D-sorganization/openflight_development/notes/2026-08-25-iwr6843-vs-kld7-upgrade-analysis.md

# Field Note: TI IWR6843 (60 GHz) vs K-LD7 (24 GHz) Upgrade Analysis

**Date:** 2026-08-25  
**Topic:** Quantitative Upgrade Significance Analysis & Upstream Discussion #161 Response  
**Author:** Dieter Olson (`dieterolson`)  
**Context:** Upstream [Discussion #161](https://github.com/jewbetcha/openflight/discussions/161) — "Is the IWR6843 upgrade significant?"

---

## 1. Executive Summary

Upstream builder `jtemple967` in Discussion #161 asked whether migrating from the dual K-LD7 radar setup to the TI IWR6843 mmWave radar is worth the effort and expense ("would be willing to upgrade if it's significant"). 

Based on empirical datasets from MLM2 Pro and TrackMan validation sessions, radar physical acoustics, and RF architecture analysis, the upgrade is **unambiguously significant**:

1. **2.58x Precision Improvement on Irons & Wedges:** Launch angle MAE improves from **2.14° (K-LD7)** to **0.83° (IWR6843)**, with a median absolute error of **0.67°**.
2. **Systematic Bias Elimination:** K-LD7 exhibited a persistent **+1.85°** upward bias; the IWR6843 LCMF-v1 pipeline centers at **-0.04°** (effectively zero bias).
3. **Driver Accuracy Improvement (3.38x):** Gated driver launch angle improves from **4.80° MAE (K-LD7)** to **1.42° MAE (IWR6843)**.
4. **Complete Physical RF Isolation:** Transitioning from 24 GHz K-band to 60 GHz V-band completely eliminates mutual RF interference and desensitization with the 24 GHz OPS243-A speed radar.
5. **Pre-Impact Club Path Extraction:** 12-channel MIMO allows 3D club path tracking (±1.18° RMSE runtime, ±0.3° fixture test), which was physically impossible with the K-LD7.
6. **Hardware & Enclosure Simplification:** 1 single board replaces 2 separate K-LD7 modules and 2 FTDI serial cables.

---

## 2. Comprehensive Hardware & RF Specifications

| Architectural Parameter | Dual K-LD7 (Deprecated) | TI IWR6843LEVM (Current Gen) | Physical Impact |
|---|---|---|---|
| **Carrier Frequency** | 24.125 GHz (K-Band) | 60.000 GHz (V-Band mmWave) | Wavelength drops from 12.4 mm to 5.0 mm; 2.5x finer spatial resolution |
| **Antenna Architecture** | 2 RX × 1 TX per unit | 4 RX × 3 TX MIMO Virtual Array | **12 virtual channels** vs single 1D phase baseline |
| **Field of View (Elevation)** | ±15° (30° span) | ±30° (60° span) | Easily captures high launch wedges (>30°) without beam clipping |
| **Field of View (Azimuth)** | ±15° (30° span) | ±60° (120° span) | Full lateral coverage for extreme pushes/pulls/shanks |
| **Doppler Resolution** | 0.85 m/s | 0.18 m/s | 4.7x finer velocity bins |
| **Velocity Aliasing Limit** | Aliased > 62 mph (100 km/h) | **Unaliased across full golf speed range (15–200+ mph)** | Eliminates fragile Doppler phase dealiasing algorithms |
| **OPS243 Coexistence** | High (both operate in 24 GHz K-band) | **Zero (60 GHz vs 24 GHz)** | Eliminates RF receiver saturation and mutual desensitization |
| **Capture Memory** | Coarse snapshot buffer over FTDI | 786 KB on-chip L3 rolling buffer | 72 ms coherent radar movie at ~4–6 ms cadence |
| **Physical Hardware** | 2 units + 2 FTDI UART bridges | 1 single board | Drastically cleaner enclosure and lower USB bus contention |

---

## 3. Empirical Accuracy Benchmarks (MLM2 Pro & TrackMan Referenced)

### 3.1 Headline Metric Summary

| Metric | Dual K-LD7 | TI IWR6843 | Delta / Improvement |
|---|---|---|---|
| **Iron/Wedge Launch Angle MAE** | 2.14° | **0.83°** | **2.58x accuracy improvement** |
| **Iron/Wedge Median Error (p50)** | 1.92° | **0.67°** | 2.87x error reduction |
| **Iron/Wedge 90th Percentile Error (p90)** | 3.95° | **1.80°** | Outliers cut by >2° |
| **Systematic Launch Bias** | +1.85° | **-0.04°** | Zero systematic bias |
| **Strict Coverage (Clean Reads)** | 72.4% | **87.4%** | +15.0% higher clean read yield |
| **Driver Launch Angle MAE (Speed-Gated)** | 4.80° | **1.42°** | **3.38x accuracy improvement** |
| **Azimuth / Launch Direction RMSE** | ±2.85° | **±1.10°** | 2.6x tighter horizontal resolution |
| **Club Path Tracking** | Unsupported | **±1.18° RMSE** | New capability |
| **Indoor Multipath Handling** | Severe ground bounce phase error | **LCMF-v1 spatial filter** | Multipath modeled and rejected |

---

### 3.2 Per-Club Empirical Breakdown

Field data captured across indoor TrackMan and MLM2 Pro cross-validation sessions:

| Club Group | Total Swings | Covered Shots | Coverage % | Launch MAE | p50 (Median) | p75 | p90 | Systematic Bias |
|---|---|---|---|---|---|---|---|---|
| **Sand Wedge** | 17 | 15 | 88.2% | **0.67°** | 0.46° | 1.06° | 1.58° | -0.22° |
| **9-Iron** | 27 | 25 | 92.6% | **0.89°** | 0.81° | 1.18° | 1.73° | +0.24° |
| **7-Iron** | 21 | 18 | 85.7% | **0.91°** | 0.49° | 1.15° | 1.88° | -0.06° |
| **5-Iron** | 22 | 18 | 81.8% | **0.82°** | 0.69° | 1.31° | 1.84° | -0.25° |
| **Driver (Raw / Ungated)** | 22 | 18 | 81.8% | 3.55° | 1.31° | 1.82° | 15.57° | +3.39° |
| **Driver (Speed-Gated)** | 22 | 15 | 68.2% | **1.42°** | 1.10° | 1.65° | 2.40° | +0.45° |
| **Mis-Hits / High Clutter** | 19 | 13 | 68.4% | **2.20°** | 1.16° | 3.07° | 5.10° | -0.54° |

---

### 3.3 Angle Source & Confidence Tier Split

The IWR6843 pipeline uses an explicit three-tier confidence architecture:

| Tier | Source / Mode | Description | Coverage | MAE | UI Representation |
|---|---|---|---|---|---|
| **Tier 1** | **Strict LCMF-v1** | High-confidence 5-model consensus over 12–18 frames in L3 buffer | 87.4% (76/87) | **0.83°** | **3 dots** (Full Confidence Measured) |
| **Tier 2** | **Relaxed RMS (≤ 0.58)** | Secondary recovery for noisier tracks passing speed & frame continuity | 85.7% (42/49) | **1.00°** | **2 dots** (Measured, Lower Confidence) |
| **Tier 2b** | **Relaxed RMS (≤ 0.70)** | Broadest recovery lane in high-clutter net environments | 91.8% (45/49) | **1.09°** | **2 dots** (Lab / Diagnostic Mode) |
| **Tier 3** | **Fallback Estimate** | Club/speed lookup table when radar movie is inconclusive | 12.6% (11/87) | **3.20°** | **1 dot / text** (Estimated) |

---

## 4. Deep-Dive: Driver Ghost-Track Gating

Why does the raw driver launch angle have a 3.55° MAE while irons achieve 0.83° MAE?

### Root Cause
Driver swings generate high-speed ball flight (140–170 mph) and large club head returns. In short indoor net cages (6–10 ft), the ball traverses the radar field in under 30 ms. In a subset of driver shots, weak radar echoes from the ball competed with secondary clutter (50–60 mph slow moving tracks from golfer hands, tee fly-off, or net rebound), leading un-gated peak detectors to lock onto the wrong target.

### Solution & Empirical Effect
By implementing an OPS-guided speed gate (requiring TI track velocity to be within ≥65–70% of the independently measured OPS243 ball speed):
- **Raw Driver MAE:** 3.55° (dominated by 4 ghost-track outliers at >15° error).
- **Speed-Gated Driver MAE:** **1.42°** (71% error reduction, median error 1.10°).
- **Outcome:** The driver error mode is solved via firmware/software gating rather than physical radar limits.

---

## 5. Drafted Response for Upstream Discussion #161

The exact response drafted for upstream Discussion #161 (`jtemple967`):

```markdown
### Is the TI IWR6843 upgrade significant compared to K-LD7?

**Short answer:** **Yes — it is a dramatic upgrade across accuracy, physical RF isolation, club tracking, and hardware complexity.**

If you are deciding whether to upgrade an existing K-LD7 build or starting a new build, here is the empirical reference data (cross-validated against MLM2 Pro and TrackMan validation sessions):

---

#### 1. Core Accuracy Comparison

| Metric | Dual K-LD7 (24 GHz) | TI IWR6843 (60 GHz) | Improvement |
|---|---|---|---|
| **Iron/Wedge Launch Angle MAE** | 2.14° | **0.83°** (p50: 0.67°) | **2.6x more accurate** (sub-1° realism) |
| **Iron Launch Angle Systematic Bias** | +1.85° (steep bias) | **-0.04°** | **Centered (near zero bias)** |
| **Iron/Wedge Coverage (Strict LCMF)** | ~70% | **87.4%** (76 / 87 shots) | +17% higher clean read rate |
| **Driver Launch Angle (Gated)** | 4.80° MAE | **1.42° MAE** | **3.4x more accurate** |
| **Azimuth / Launch Direction RMSE** | ±2.85° | **±1.10°** | 2.6x tighter horizontal resolution |
| **Club Path Extraction** | Not physically possible | **Supported (±1.18° RMSE)** | Full pre-impact club trajectory |
| **OPS243 Radar Coexistence** | High mutual RF cross-talk (both 24 GHz) | **Zero cross-talk (60 GHz vs 24 GHz)** | Complete physical RF isolation |
| **Hardware Footprint** | 2 modules + 2 FTDI adapters | **1 single board** (IWR6843LEVM) | Much simpler enclosure & wiring |

---

#### 2. Empirical Breakdown by Club (IWR6843 Reference Data)

| Club | Good Shots | Covered | Coverage % | MAE | p50 (Median) | p90 | Bias |
|---|---|---|---|---|---|---|---|
| **Sand Wedge** | 17 | 15 | 88.2% | **0.67°** | 0.46° | 1.58° | -0.22° |
| **9-Iron** | 27 | 25 | 92.6% | **0.89°** | 0.81° | 1.73° | +0.24° |
| **7-Iron** | 21 | 18 | 85.7% | **0.91°** | 0.49° | 1.88° | -0.06° |
| **5-Iron** | 22 | 18 | 81.8% | **0.82°** | 0.69° | 1.84° | -0.25° |
| **Driver (Raw / Ungated)** | 22 | 18 | 81.8% | 3.55° | 1.31° | 15.57° | +3.39° |
| **Driver (Speed-Gated)** | 22 | 15 | 68.2% | **1.42°** | 1.10° | 2.40° | +0.45° |

---

#### 3. Why the Physical Difference Is So Large

1. **60 GHz mmWave Wavelength (5.0 mm vs 12.4 mm):** Shorter wavelength enables much finer spatial phase separation in indoor net distances (3–8 ft).
2. **12 Virtual Channel MIMO Array (4 RX × 3 TX):** K-LD7 provided only a single 1D phase baseline (2 RX × 1 TX). The IWR6843 provides true 3D spatial resolution for both vertical launch angle and horizontal aim.
3. **L3 Rolling Buffer & LCMF-v1 Fusion:** The IWR6843 captures a 72 ms coherent radar movie (12–18 frames at ~4–6 ms cadence). Five physics judges independently model direct vs ground-bounce multipath, discarding impact clutter and using clean late flight.
4. **RF Isolation:** Operating at 60 GHz completely eliminates the mutual desensitization and RF jamming that occurred when running K-LD7 and OPS243-A in the same 24 GHz K-band.

---

#### 4. Honest Caveats
- **Driver Ghost Tracks:** Without speed gating, driver can false-accept slow ghost echoes (55 mph club/rebound reflections vs 150+ mph ball). Enabling the OPS-guided speed gate brings driver MAE down to 1.42°.
- **Setup Geometry Matters:** Because mmWave phase is precise, measuring your physical mount tilt (~12.4°) and tee distance accurately is critical for sub-degree accuracy.

#### 5. Practical Recommendation
- **New Builders:** Build with the **TI IWR6843LEVM**. Do not purchase K-LD7s.
- **Existing K-LD7 Owners:** Upgrading is **well worth it** if you want realistic iron/wedge ball flights into a net (<1° error), pre-impact club path data, and a cleaner single-board enclosure.
```

---

## 6. Recommendations for Builders & Contributors

1. **Deprecation Status:** K-LD7 code remains supported for legacy builds in `src/openflight/kld7/`, but active feature work and tuning is 100% focused on IWR6843 mmWave.
2. **Firmware Road:** The production 18-frame 3-TX firmware (`l3_dump.c`) delivers rock-solid <1° iron accuracy. Upcoming work on `feat/club-path-iwr` (25 frames) will extend pre-impact club tracking.
3. **Truth Data Protocol:** Future validation sessions should continue following `validation/mlm2pro-cross-validation.md` to feed continuous truth data back into LCMF-v1 tuning.
