D-sorganization/openflight_development/cad/IARC_case/step/monitor_back.step

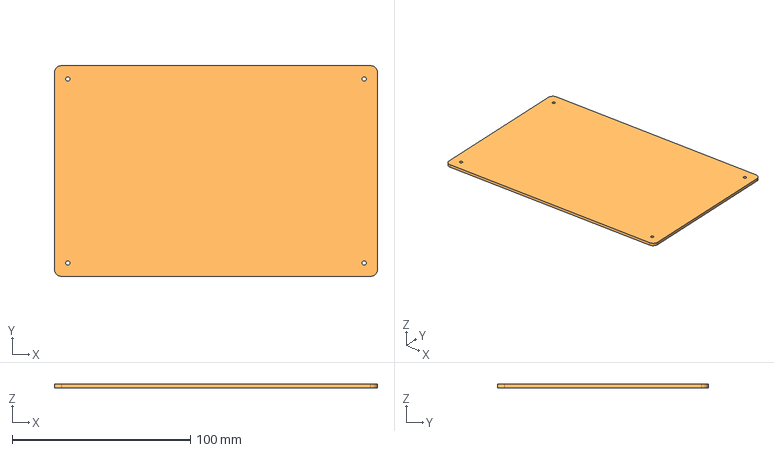
[picture p43: CAD file, 2026-08-24]
cad/IARC_case/step/monitor_back.step
181.0 x 118.0 x 2.00 mm
