D-sorganization/openflight_development/cad/IARC_case/step/monitor_mount.step

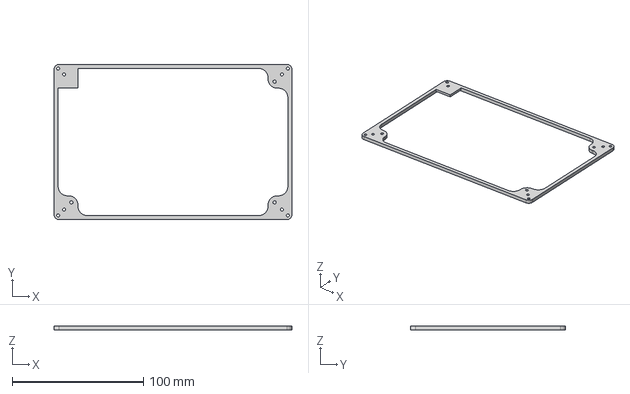
[picture p44: CAD file, 2026-08-24]
cad/IARC_case/step/monitor_mount.step
181.4 x 118.4 x 3.00 mm
