D-sorganization/openflight_development/cad/IARC_case/step/name_plate.step

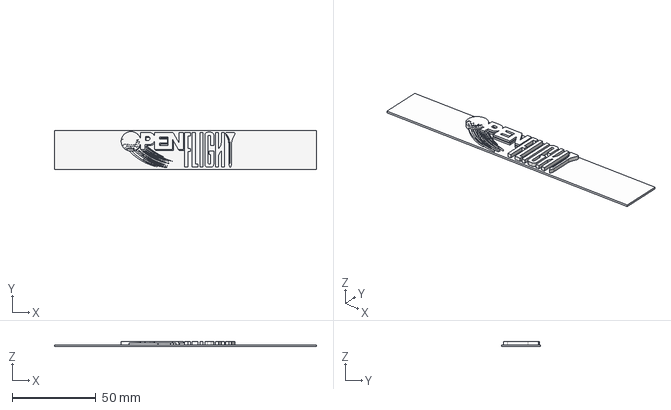
[picture p45: CAD file, 2026-08-24]
cad/IARC_case/step/name_plate.step
156.6 x 23.2 x 3.00 mm
