D-sorganization/openflight_development/cad/IARC_case/step/KLD7_h_mount_R_v2.step

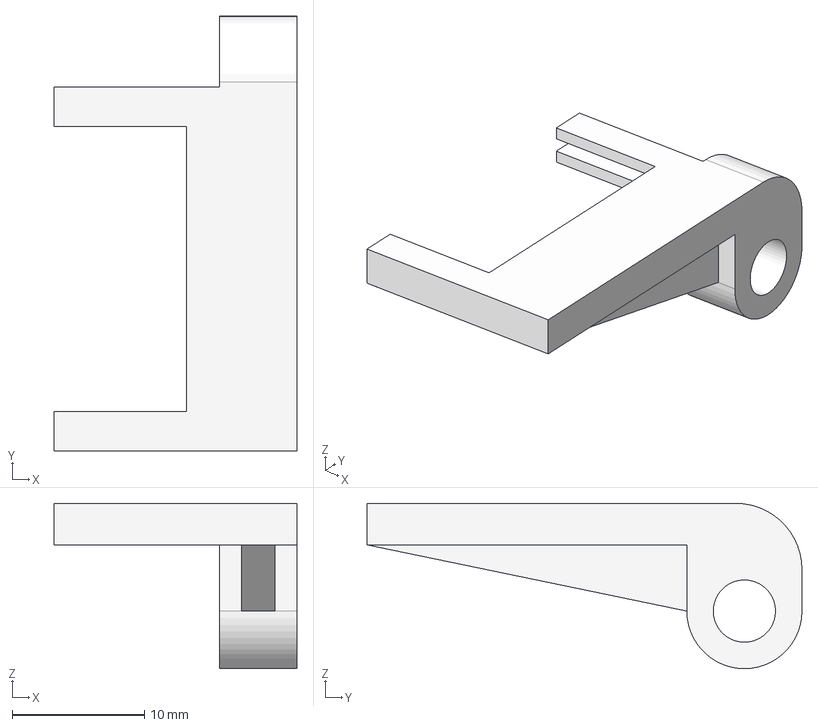
[picture p46: CAD file, 2026-08-24]
cad/IARC_case/step/KLD7_h_mount_R_v2.step
18.3 x 32.8 x 12.5 mm
