D-sorganization/openflight_development/scripts/analysis/replay_captures.py

#!/usr/bin/env python3
"""
Replay raw I/Q captures from session logs through the FFT pipeline.

Reads rolling_buffer_capture entries from a session JSONL file, runs each
through the processor, and prints detailed FFT analysis showing what the
processor sees at each step. This is the primary tool for debugging why
real golf swings aren't being detected.

Usage:
    uv run python scripts/replay_captures.py session_logs/session_*.jsonl
    uv run python scripts/replay_captures.py session_logs/session_*.jsonl --capture 3
    uv run python scripts/replay_captures.py session_logs/session_*.jsonl --fft-detail
"""

import argparse
import json
import sys
from pathlib import Path

import numpy as np

# Add project root to path
sys.path.insert(0, str(Path(__file__).parent.parent / "src"))

from openflight.rolling_buffer.processor import RollingBufferProcessor
from openflight.rolling_buffer.types import IQCapture


def load_captures(filepath: str) -> list[dict]:
    """Load rolling_buffer_capture entries from a JSONL session file."""
    captures = []
    with open(filepath) as f:
        for line_num, line in enumerate(f, 1):
            line = line.strip()
            if not line:
                continue
            try:
                entry = json.loads(line)
                if entry.get("type") == "rolling_buffer_capture":
                    entry["_line"] = line_num
                    captures.append(entry)
            except json.JSONDecodeError:
                continue
    return captures


def analyze_block_detail(processor: RollingBufferProcessor, i_block, q_block, block_idx: int):
    """Run FFT on a single block and print detailed spectrum info."""
    i_block = np.array(i_block, dtype=np.float64)
    q_block = np.array(q_block, dtype=np.float64)

    # Reproduce the processor's pipeline step by step
    i_centered = i_block - np.mean(i_block)
    q_centered = q_block - np.mean(q_block)
    i_scaled = i_centered * (processor.VOLTAGE_REF / processor.ADC_RANGE)
    q_scaled = q_centered * (processor.VOLTAGE_REF / processor.ADC_RANGE)
    i_windowed = i_scaled * processor.hanning_window
    q_windowed = q_scaled * processor.hanning_window
    complex_signal = i_windowed + 1j * q_windowed

    fft_result = np.fft.fft(complex_signal, processor.FFT_SIZE)
    magnitude = np.abs(fft_result)

    half = processor.FFT_SIZE // 2
    dc_mask = processor.DC_MASK_BINS

    # Find top 5 peaks in positive frequencies (outbound)
    pos_mags = magnitude[1:half].copy()
    pos_peaks = []
    for _ in range(5):
        idx = np.argmax(pos_mags) + 1  # +1 because we start from bin 1
        mag = pos_mags[idx - 1]
        if mag < 1.0:
            break
        freq_hz = idx * processor.SAMPLE_RATE / processor.FFT_SIZE
        speed_mps = freq_hz * processor.WAVELENGTH_M / 2
        speed_mph = speed_mps * processor.MPS_TO_MPH
        masked = idx < dc_mask
        pos_peaks.append((idx, mag, speed_mph, masked))
        # Zero out nearby bins to find next peak
        lo = max(0, idx - 1 - 20)
        hi = min(half - 1, idx - 1 + 20)
        pos_mags[lo:hi] = 0

    # Find top 5 peaks in negative frequencies (inbound)
    neg_start = half + 1
    neg_end = processor.FFT_SIZE - dc_mask
    neg_mags = magnitude[neg_start:neg_end].copy() if neg_start < neg_end else np.array([])
    neg_peaks = []
    for _ in range(5):
        if len(neg_mags) == 0:
            break
        idx_rel = np.argmax(neg_mags)
        mag = neg_mags[idx_rel]
        if mag < 1.0:
            break
        abs_bin = idx_rel + neg_start
        freq_bin = processor.FFT_SIZE - abs_bin
        freq_hz = freq_bin * processor.SAMPLE_RATE / processor.FFT_SIZE
        speed_mps = freq_hz * processor.WAVELENGTH_M / 2
        speed_mph = speed_mps * processor.MPS_TO_MPH
        neg_peaks.append((abs_bin, mag, speed_mph, False))
        lo = max(0, idx_rel - 20)
        hi = min(len(neg_mags), idx_rel + 20)
        neg_mags[lo:hi] = 0

    # Also check what's in the DC-masked negative region (near bin FFT_SIZE-1)
    dc_neg_mags = magnitude[processor.FFT_SIZE - dc_mask :] if dc_mask > 0 else np.array([])
    dc_neg_peak_mag = np.max(dc_neg_mags) if len(dc_neg_mags) > 0 else 0
    dc_neg_peak_bin = (
        np.argmax(dc_neg_mags) + (processor.FFT_SIZE - dc_mask) if len(dc_neg_mags) > 0 else 0
    )

    timestamp_ms = (block_idx * processor.STEP_SIZE_STANDARD / processor.SAMPLE_RATE) * 1000

    print(f"  Block {block_idx:3d} (t={timestamp_ms:6.1f}ms):")

    if pos_peaks:
        print("    OUTBOUND (pos freq) top peaks:")
        for bin_idx, mag, speed, masked in pos_peaks:
            mask_tag = " [DC MASKED]" if masked else ""
            thresh_tag = " [< threshold]" if mag < processor.MAGNITUDE_THRESHOLD else ""
            print(f"      bin {bin_idx:5d}  mag {mag:8.1f}  {speed:6.1f} mph{mask_tag}{thresh_tag}")
    else:
        print("    OUTBOUND: no peaks above 1.0")

    if neg_peaks:
        print("    INBOUND (neg freq) top peaks:")
        for bin_idx, mag, speed, masked in neg_peaks:
            thresh_tag = " [< threshold]" if mag < processor.MAGNITUDE_THRESHOLD else ""
            print(f"      bin {bin_idx:5d}  mag {mag:8.1f}  {speed:6.1f} mph{thresh_tag}")
    else:
        print("    INBOUND: no peaks above 1.0")

    if dc_neg_peak_mag > 1.0:
        freq_bin = processor.FFT_SIZE - dc_neg_peak_bin
        speed_mps = (
            freq_bin * processor.SAMPLE_RATE / processor.FFT_SIZE * processor.WAVELENGTH_M / 2
        )
        speed_mph = speed_mps * processor.MPS_TO_MPH
        print(
            f"    DC-MASKED NEG: bin {dc_neg_peak_bin} mag {dc_neg_peak_mag:.1f} ({speed_mph:.1f} mph)"
        )
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
